Qirab/QirabConservationCradle/3DPRINT/3MF/QCC Box Lid QCC44.3mf

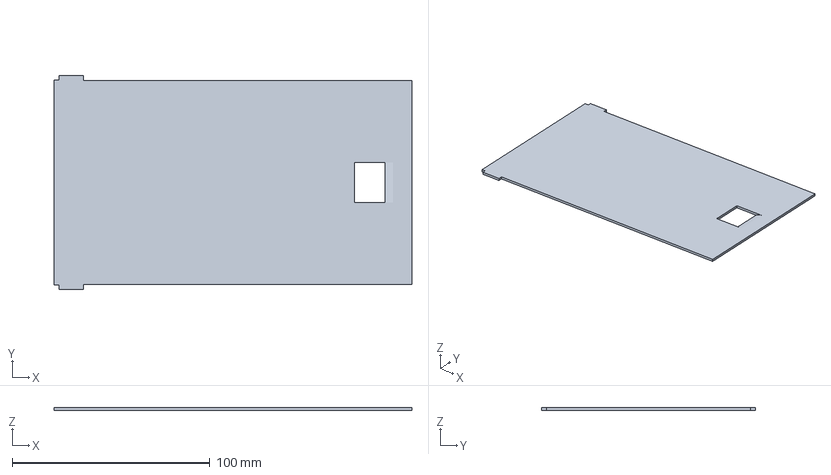
[picture p16: CAD file, 2025-01-16]
3DPRINT/3MF/QCC Box Lid QCC44.3mf
181.0 x 108.0 x 1.50 mm
