Qirab/QirabConservationCradle/3DPRINT/3MF/QCC Box QCC50.3mf

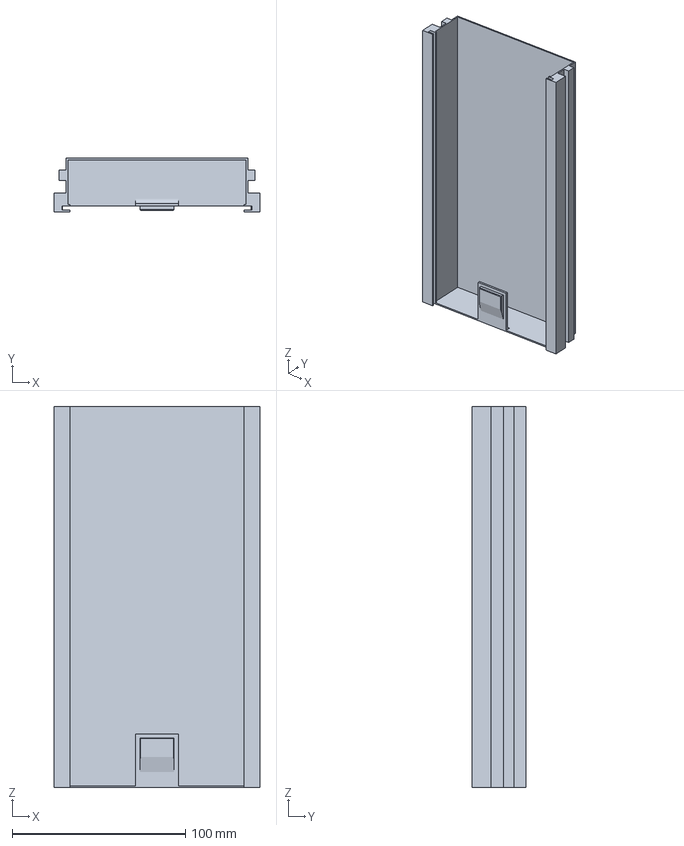
[picture p17: CAD file, 2025-01-16]
3DPRINT/3MF/QCC Box QCC50.3mf
118.8 x 31.0 x 220.0 mm
