Qirab/QirabConservationCradle/3DPRINT/3MF/QCC Foot Lower.3mf

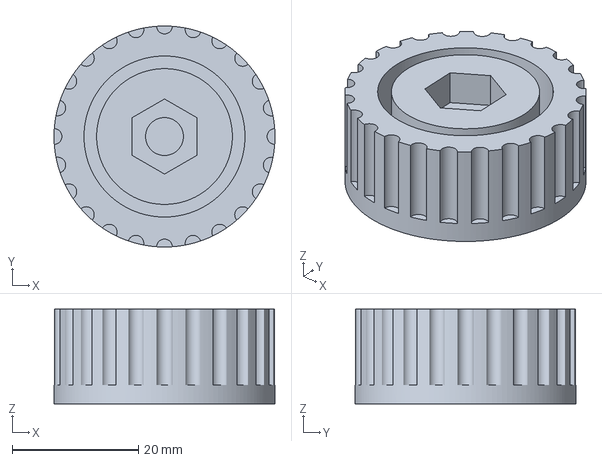
[picture p18: CAD file, 2025-01-16]
3DPRINT/3MF/QCC Foot Lower.3mf
35.0 x 35.0 x 15.0 mm
