Qirab/QirabConservationCradle/3DPRINT/3MF/QCC Box QCC44.3mf

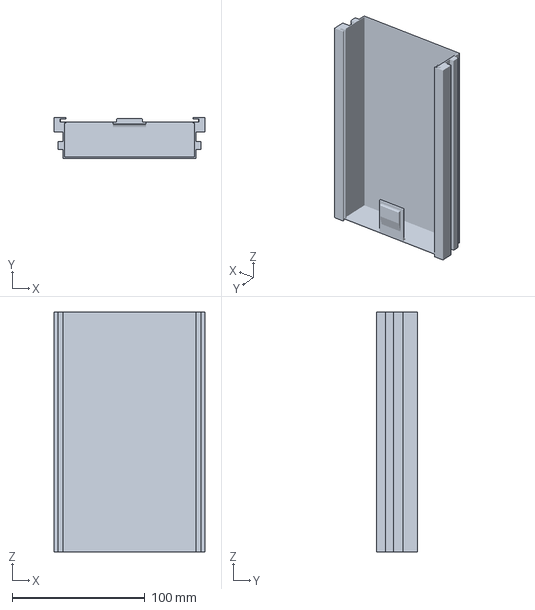
[picture p19: CAD file, 2025-01-16]
3DPRINT/3MF/QCC Box QCC44.3mf
113.8 x 31.0 x 181.0 mm
