Qirab/QirabConservationCradle/PDF/QCC50/QCC50 v2.3 ALUMINUM.pdf

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

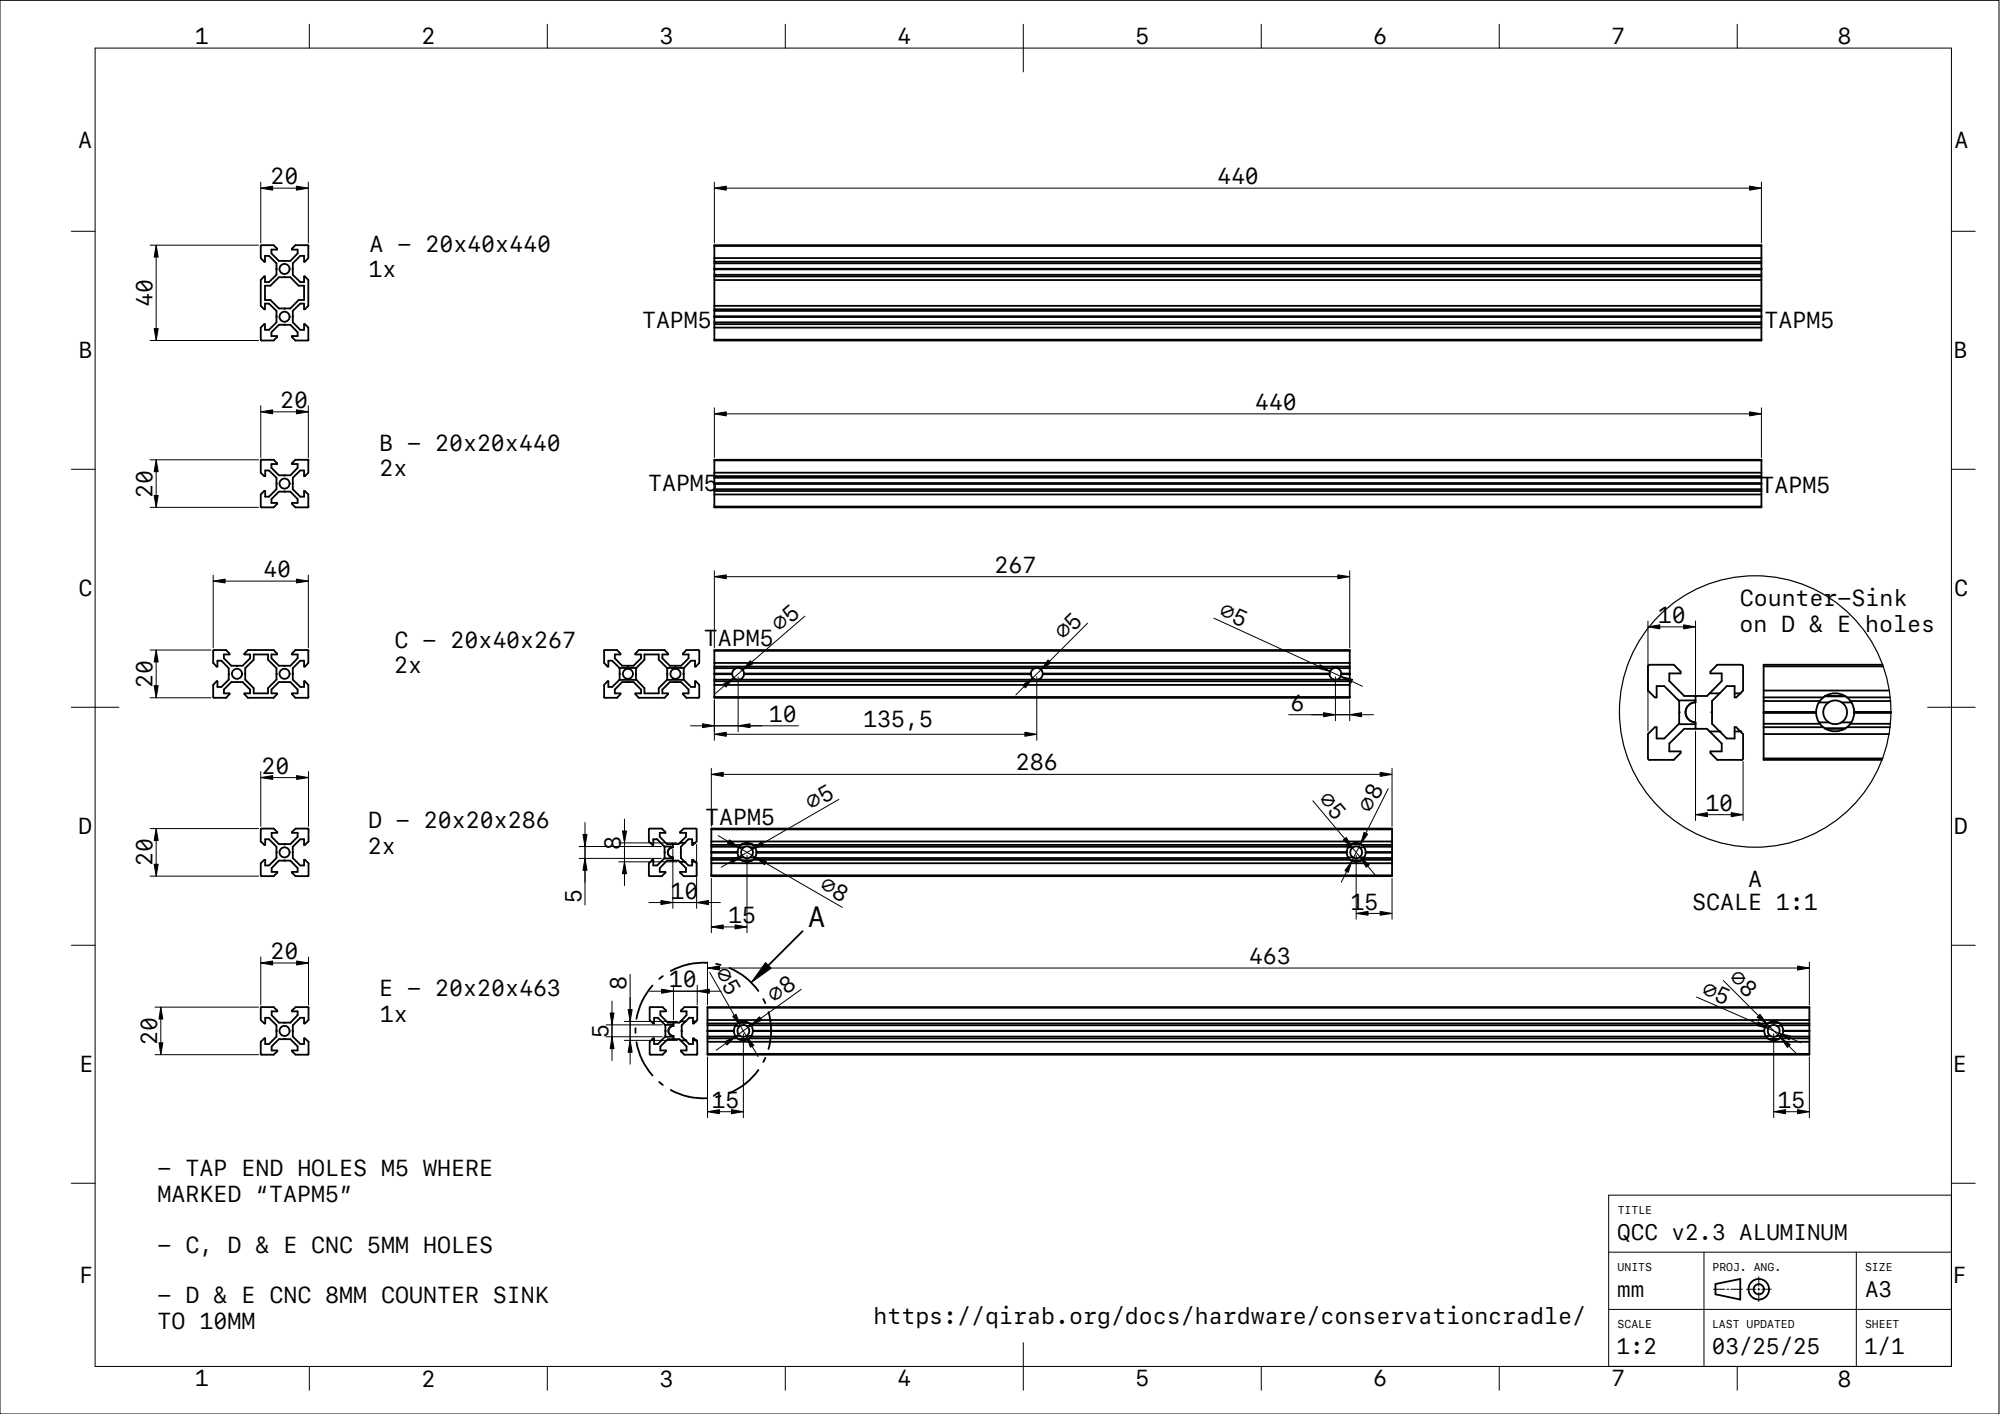
[picture p32: page 1]
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
