Qirab/QirabConservationCradle/PDF/QCC44/QCC44 v2.1_002AFD6B-C673-4160-8CCF-45D82DDA380A.pdf

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

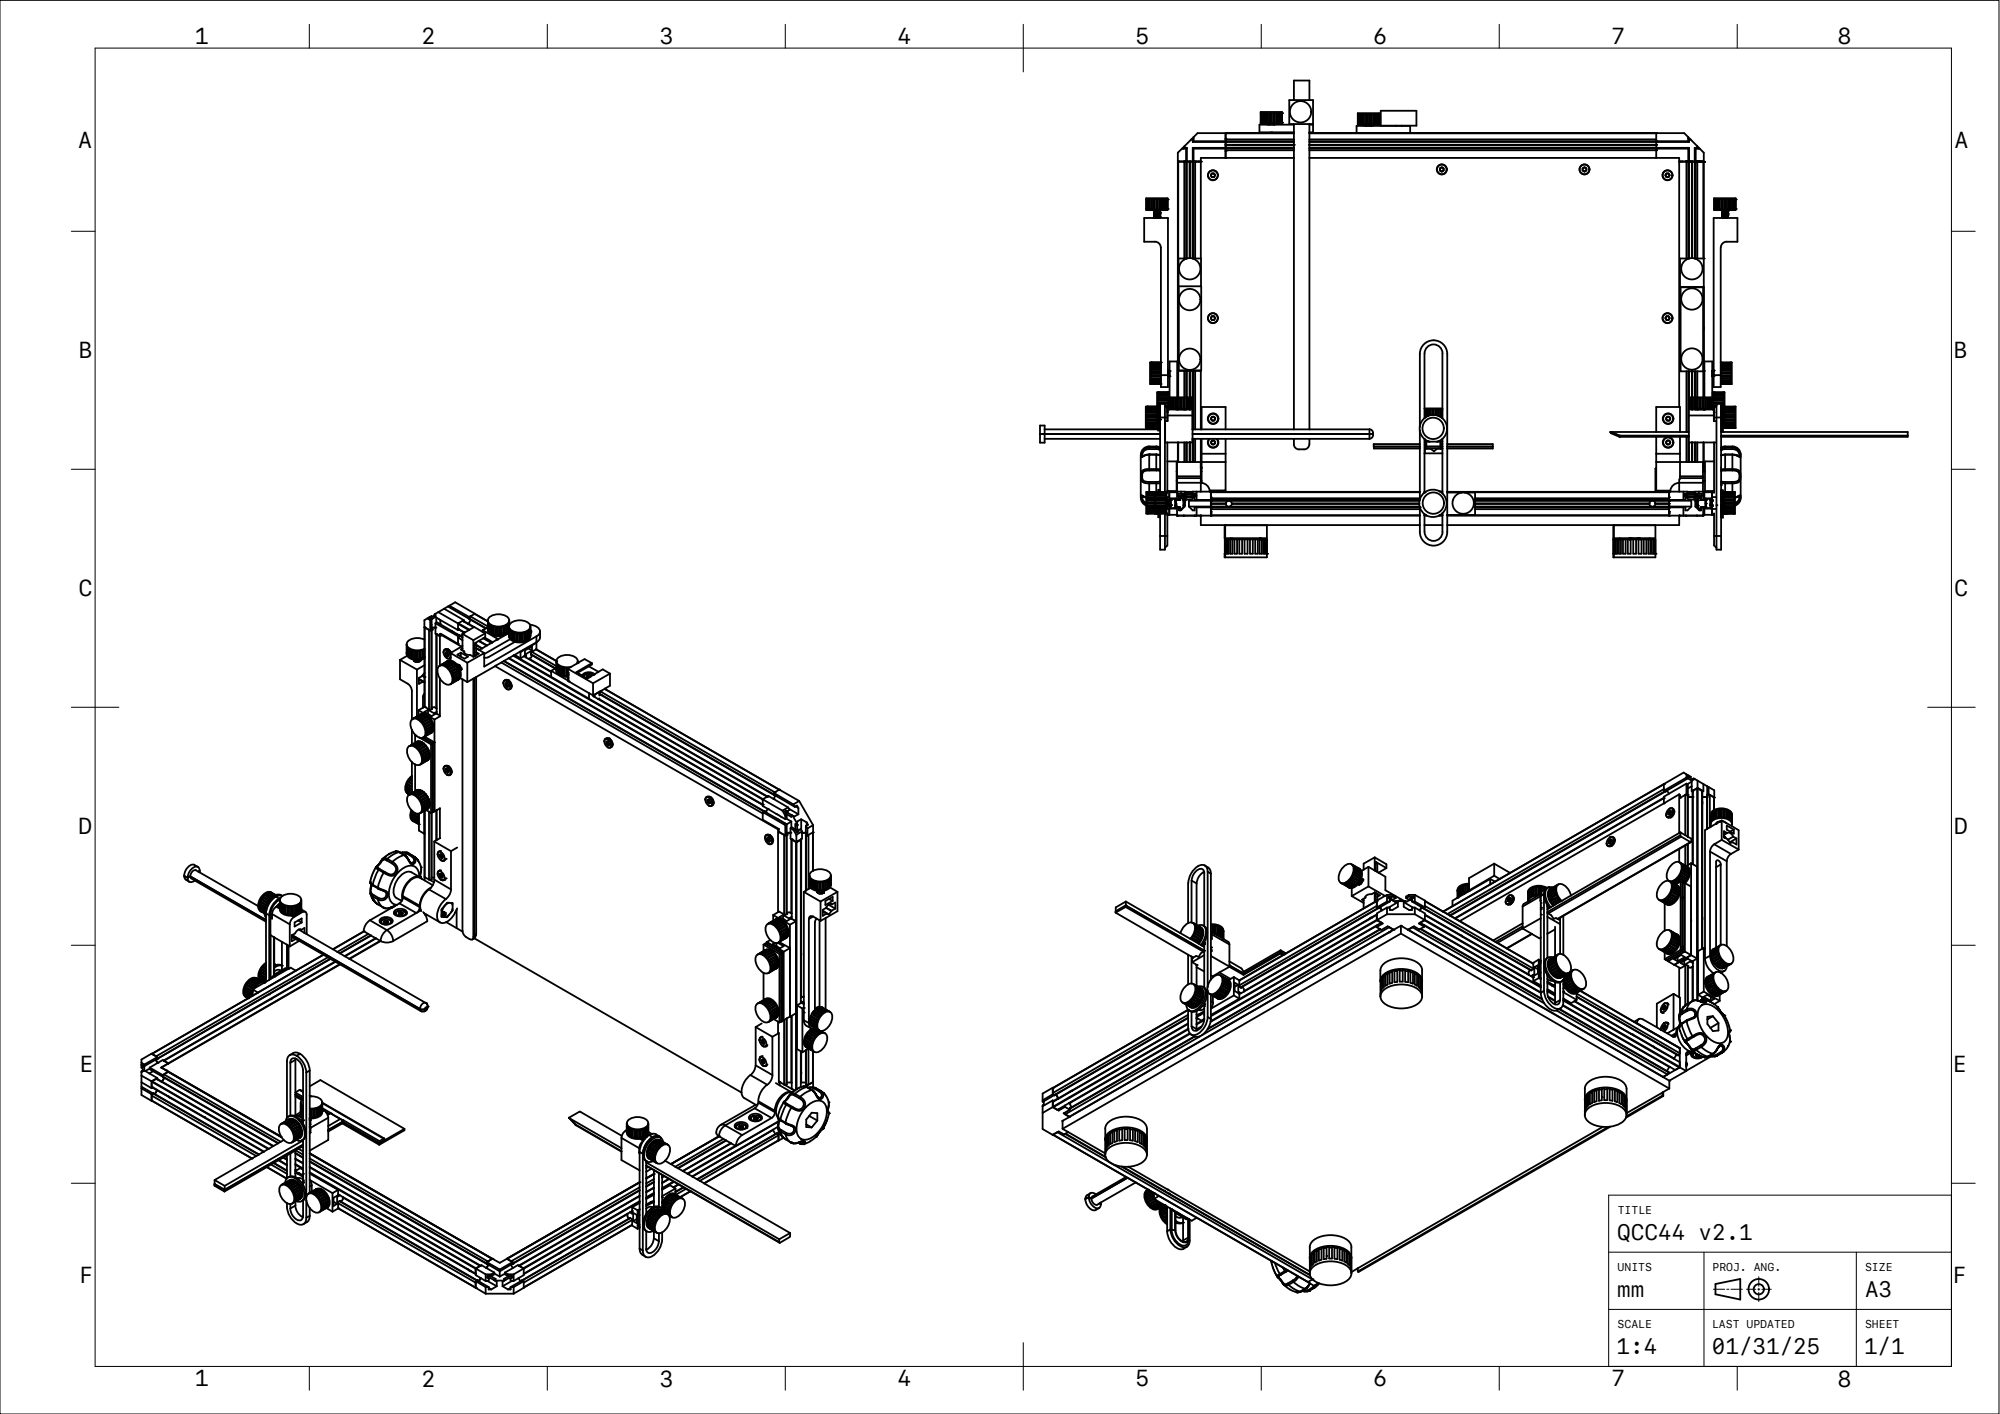
[picture p33: page 1]
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
