Qirab/QirabConservationCradle/PDF/QCC44/QCC44 v2.1_AB25C356-3EBE-400D-AA87-4F2AF94994CF.pdf

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

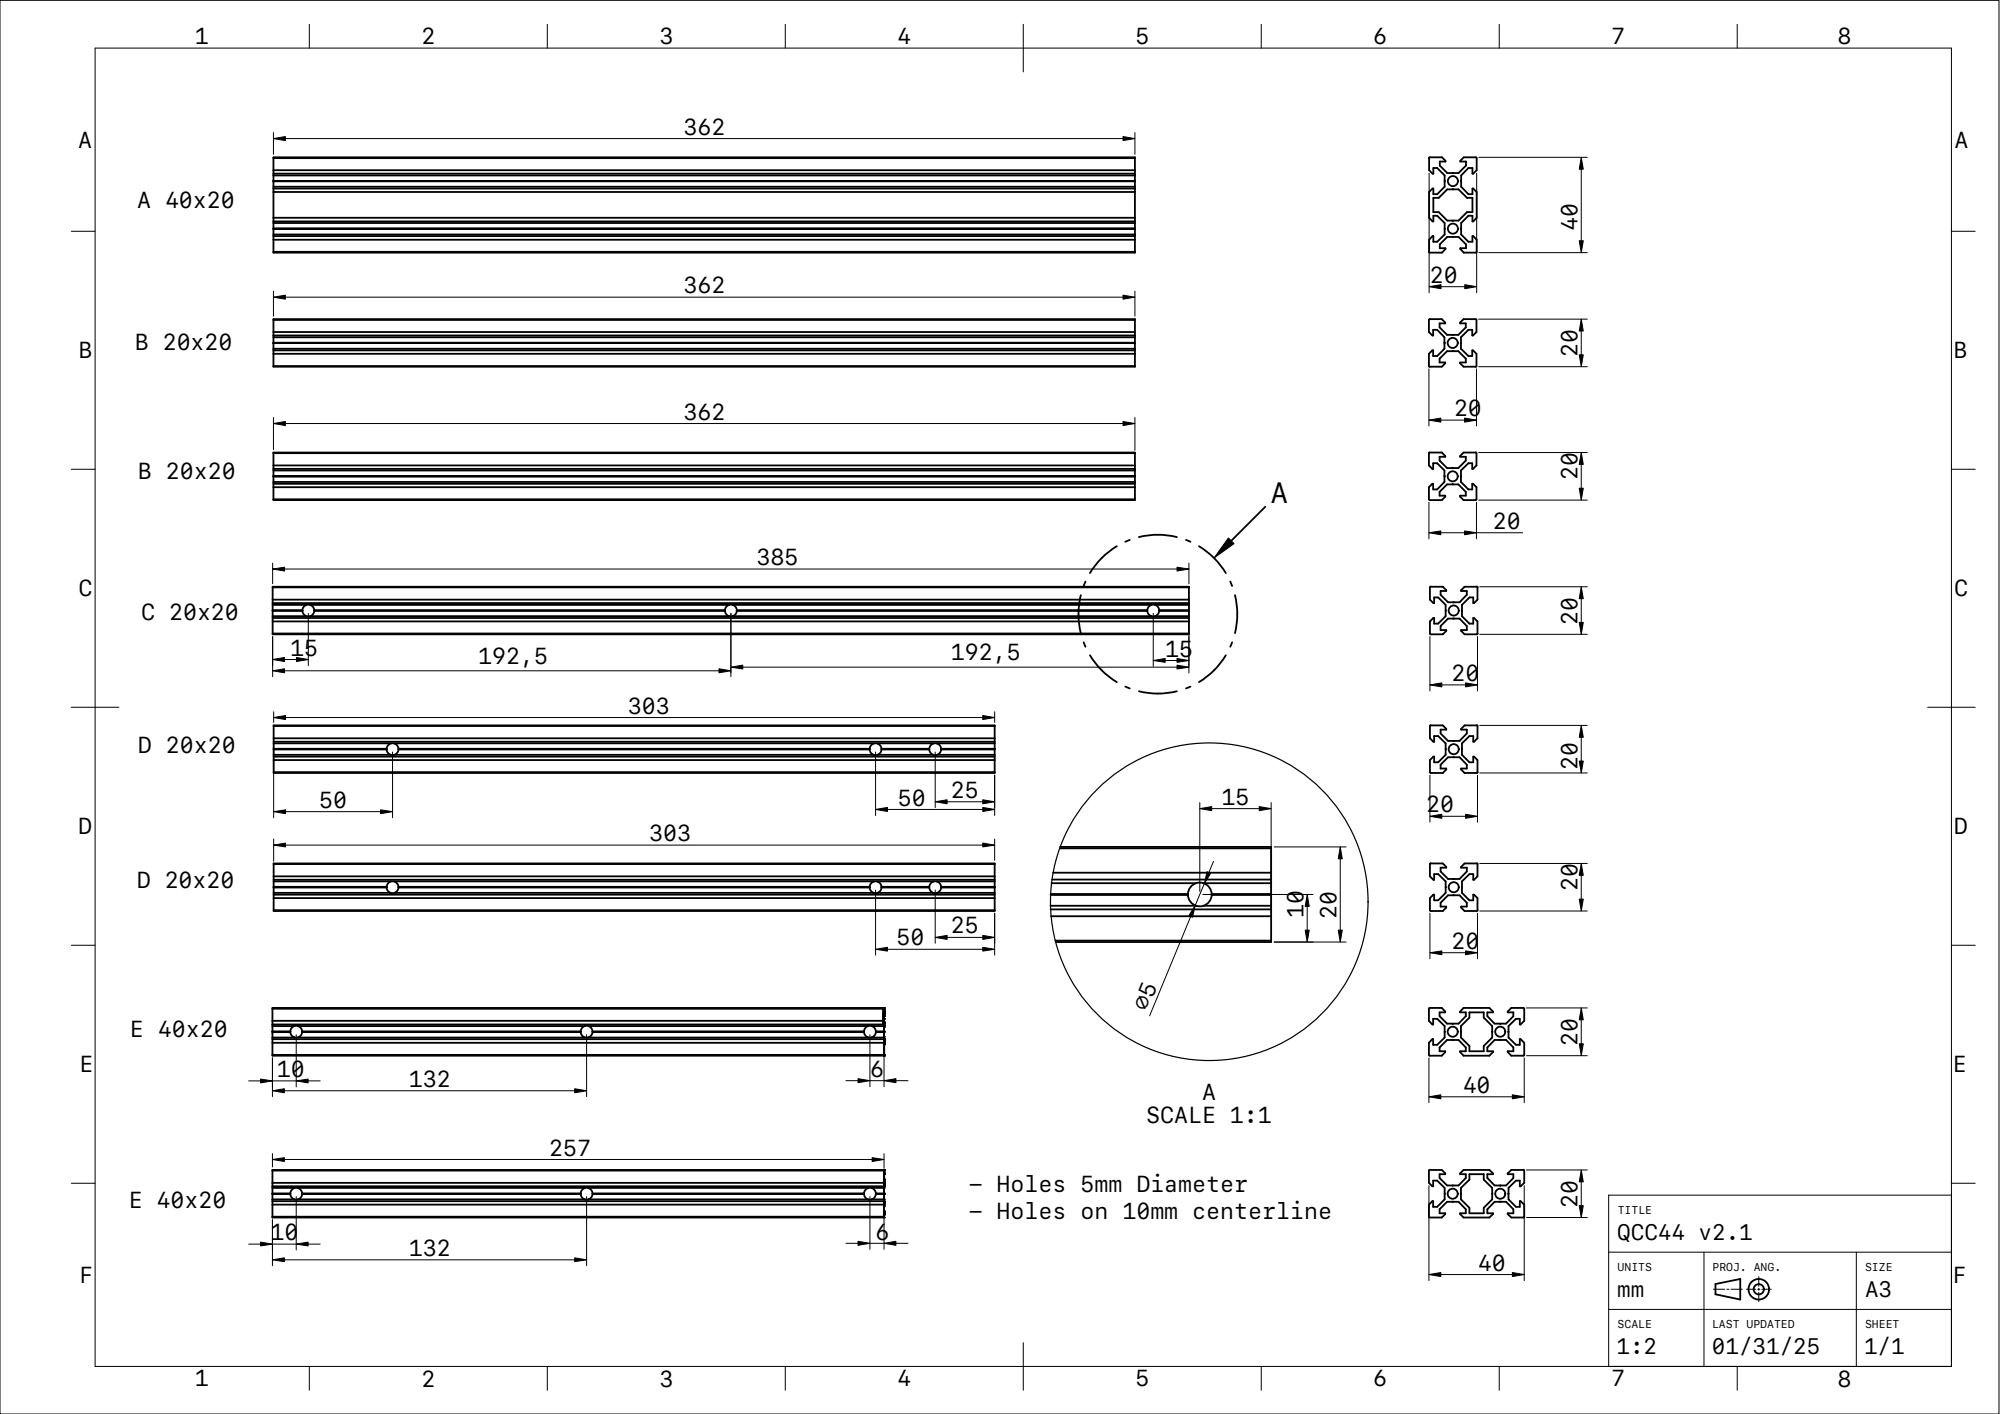
[picture p34: page 1]
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
