Qirab/QirabConservationCradle/PDF/QCC70/QCC70 v2.3 ALUMINUM.pdf

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

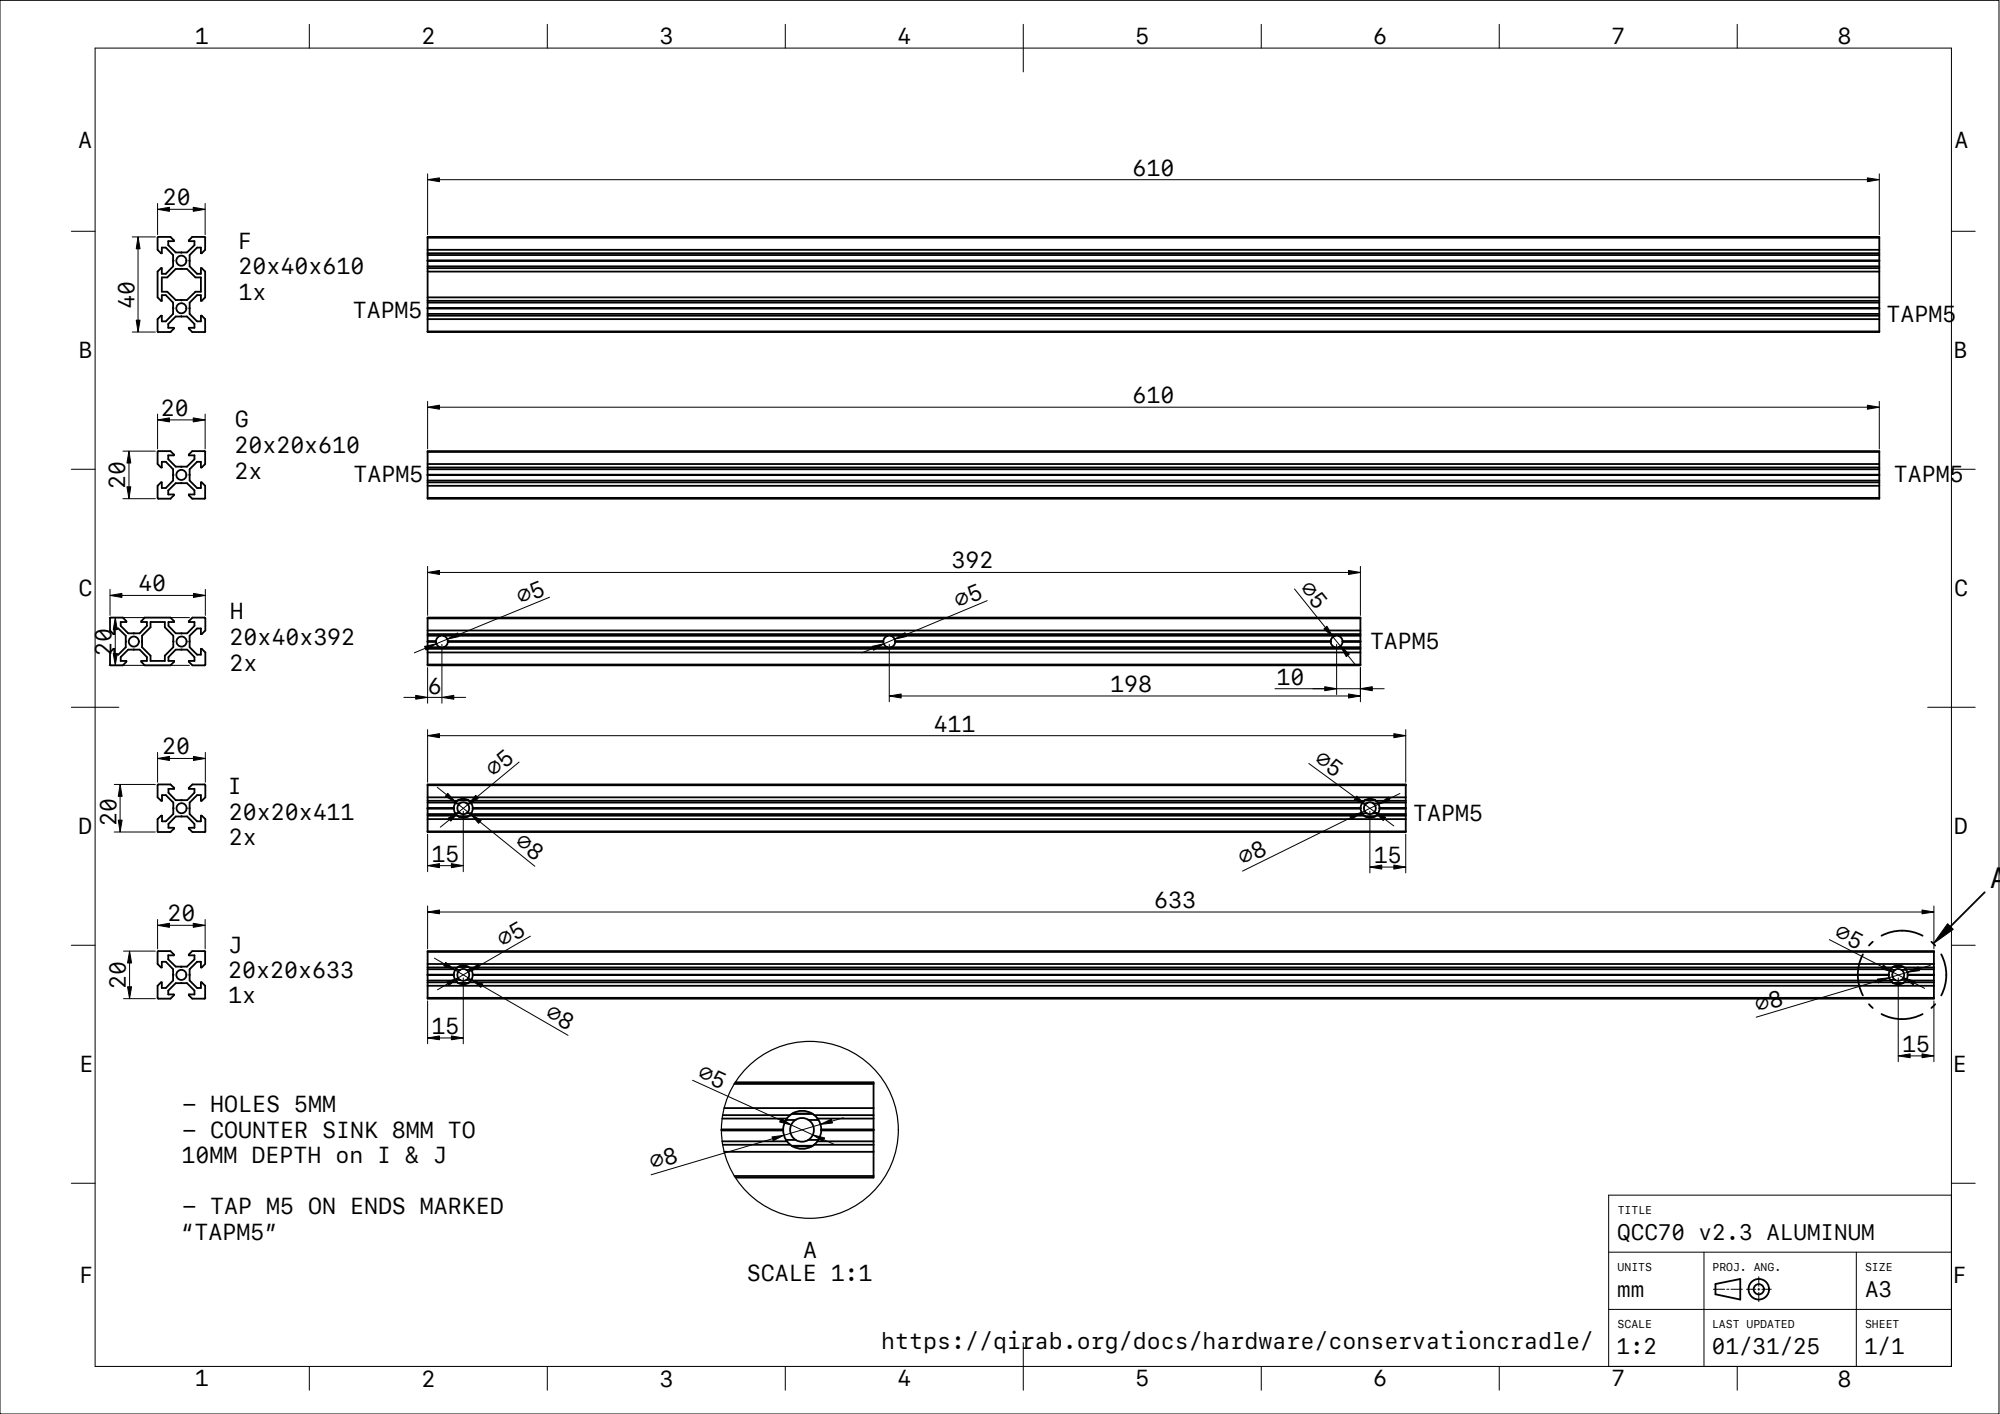
[picture p35: page 1]
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
